charles-waite/ESP32-Matter-Environmental-Sensor/components/oled_ssd1306_tp/resources/DemoFrame2.jpg

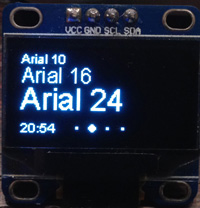
components/oled_ssd1306_tp/resources/DemoFrame2.jpg
