charles-waite/ESP32-Matter-Environmental-Sensor/components/oled_ssd1306_tp/resources/DemoFrame4.jpg

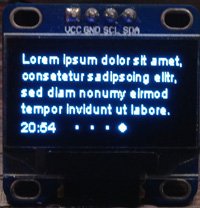
components/oled_ssd1306_tp/resources/DemoFrame4.jpg
