charles-waite/ESP32-Matter-Environmental-Sensor/main/chip_project_config.h

#pragma once

#define CHIP_DEVICE_CONFIG_DEVICE_VENDOR_NAME "Waite Design Labs"
#define CHIP_DEVICE_CONFIG_DEVICE_PRODUCT_NAME "WALL-Env Sensor"
#define CHIP_DEVICE_CONFIG_DEVICE_SOFTWARE_VERSION_STRING "0.6.0"
#define CHIP_DEVICE_CONFIG_DEFAULT_DEVICE_HARDWARE_VERSION_STRING "1.0"
