charles-waite/ESP32-Matter-Environmental-Sensor/components/BME68x_Sensor_library/examples/forced_mode/forced_mode.ino

/**
 * Copyright (C) 2021 Bosch Sensortec GmbH
 *
 * SPDX-License-Identifier: BSD-3-Clause
 * 
 */

#include "Arduino.h"
#include "bme68xLibrary.h"

#ifndef PIN_CS
#define PIN_CS SS
#endif

Bme68x bme;

/**
 * @brief Initializes the sensor and hardware settings
 */
void setup(void)
{
	SPI.begin();
	Serial.begin(115200);
	
	while (!Serial)
		delay(10);
		
	/* initializes the sensor based on SPI library */
	bme.begin(PIN_CS, SPI);

	if(bme.checkStatus())
	{
		if (bme.checkStatus() == BME68X_ERROR)
		{
			Serial.println("Sensor error:" + bme.statusString());
			return;
		}
		else if (bme.checkStatus() == BME68X_WARNING)
		{
			Serial.println("Sensor Warning:" + bme.statusString());
		}
	}
	
	/* Set the default configuration for temperature, pressure and humidity */
	bme.setTPH();

	/* Set the heater configuration to 300 deg C for 100ms for Forced mode */
	bme.setHeaterProf(300, 100);

	Serial.println("TimeStamp(ms), Temperature(deg C), Pressure(Pa), Humidity(%), Gas resistance(ohm), Status");
}

void loop(void)
{
	bme68xData data;

	bme.setOpMode(BME68X_FORCED_MODE);
	delayMicroseconds(bme.getMeasDur());

	if (bme.fetchData())
	{
		bme.getData(data);
		Serial.print(String(millis()) + ", ");
		Serial.print(String(data.temperature) + ", ");
		Serial.print(String(data.pressure) + ", ");
		Serial.print(String(data.humidity) + ", ");
		Serial.print(String(data.gas_resistance) + ", ");
		Serial.println(data.status, HEX);
	}
}
