charles-waite/ESP32-Matter-Environmental-Sensor/components/bsec2/examples/bme68x_demo_sample/sensor_manager.h

/*!
 * Copyright (c) 2021 Bosch Sensortec GmbH. All rights reserved.
 *
 * BSD-3-Clause
 *
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
 * 1. Redistributions of source code must retain the above copyright
 *    notice, this list of conditions and the following disclaimer.
 *
 * 2. Redistributions in binary form must reproduce the above copyright
 *    notice, this list of conditions and the following disclaimer in the
 *    documentation and/or other materials provided with the distribution.
 *
 * 3. Neither the name of the copyright holder nor the names of its
 *    contributors may be used to endorse or promote products derived from
 *    this software without specific prior written permission.
 *
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
 * @file	sensor_manager.h
 * @date	03 Jan 2024
 * @version	2.1.5
 * 
 * @brief	Header file for the sensor manager
 * 
 * 
 */

#ifndef SENSOR_MANAGER_H
#define SENSOR_MANAGER_H

/* Include of Arduino Core */
#include <Arduino.h>
#include <SdFat.h>
#include <RTClib.h>
#include <ArduinoJson.h>
#include <SPI.h>
#include <Wire.h>
#include "utils.h"
#include "demo_app.h"
#include <bme68xLibrary.h>
#include <commMux\commMux.h>

/* I2C-Expander masks */
#define I2C_EXPANDER_ADDR 				0x20
#define I2C_EXPANDER_OUTPUT_REG_ADDR 	0x01
#define I2C_EXPANDER_CONFIG_REG_ADDR 	0x03
#define I2C_EXPANDER_CONFIG_REG_MASK 	0x00
#define SPI_COMM_SPEED 					UINT32_C(4000000)
#define NUM_BME68X_UNITS				UINT8_C(8)
#define HEATER_TIME_BASE				UINT8_C(140)
#define MAX_HEATER_DURATION				UINT8_C(200)
#define GAS_WAIT_SHARED					UINT8_C(140)
/* Size of Json document in bytes */
#define JSON_DOC_SIZE 					UINT16_C(5000)

/*!
 * @brief : Class library that holds the functionality of the sensor manager
 */
class sensorManager
{
private:
	static bme68x_sensor _sensors[NUM_BME68X_UNITS];
	Bme68x 				bme68xSensors[NUM_BME68X_UNITS];
	bme68x_data 		 _field_data[3];

	StaticJsonDocument<JSON_DOC_SIZE>	_configDoc;
	
	/*!
	 * @brief : This function initializes the given BME688 sensor
	 * 
	 * @param[in] sensorNumber 	: The sensor number
	 * @param[in] sensorId 		: The sensor id
     * 
     * @return 0 on success, lessthan zero otherwise
	 */
	int8_t initialize_sensor(uint8_t sensor_number, uint32_t& sensor_id);
	/*!
	 * @brief : This function configures the heater settings of the sensor
	 * 
	 * @param[in] heaterProfileStr 	: The heater profile string id
	 * @param[in] dutyCycleStr 		: The duty cycle string id
	 * @param[in] heaterProfile 	: The heater profile structure
	 * @param[in] sensorNumber 		: The sensor number
     * 
     * @return  bme68x return code
	 */
	int8_t set_heater_profile(const String& heater_profile_str, const String& duty_cycle_str, 
	                        bme68x_heater_profile& heater_profile, uint8_t sensor_number);
	
	/*!
	 * @brief : This function configures the bme688 sensor
	 * 
	 * @param[in] heaterProfile : The heater profile structure
	 * @param[in] sensorNumber 	: The sensor number
     * 
     * @return  bme68x return code
	 */
	int8_t configure_sensor(bme68x_heater_profile& heater_profile, uint8_t sensor_number);
public:
	/*!
	 * @brief : This function retrieves the selected sensor.
	 * 
	 * @param[in] num : Sensor number
     * 
     * @return  Pointer to sensor if it exists, else nullptr
	 */
	static inline bme68x_sensor* get_sensor(uint8_t num)
	{
		bme68x_sensor* sensor = nullptr;

		if (num < NUM_BME68X_UNITS)
		{
			sensor = &_sensors[num];
		}
		return sensor;
	};
	
	/*!
	 * @brief : This function selects next readable bme688 sensor in given operation mode
	 * 
	 * @param[inout] num	: Reference to the sensor number
	 * @param[in] mode		: The sensor operation mode
     * 
     * @return  True if available
	 */
	static inline bool select_next_sensor(uint64_t& wake_up_time, uint8_t& num, uint8_t mode)
	{
		num = (uint8_t)0xFF;

		for (uint8_t i = 0; i < NUM_BME68X_UNITS; i++)
		{

			if ((_sensors[i].mode == mode) && (_sensors[i].wake_up_time < wake_up_time))
			{
				wake_up_time = _sensors[i].wake_up_time;
				num = i;
			}
		}
		
		if (num < NUM_BME68X_UNITS)
		{
			return true;
		}
		return false;
	}
	
	/*!
	 * @brief : This function schedules the next readable bme688 sensor
	 * 
	 * @param[inout] num : Reference to the sensor number
     * 
     * @return  True if available
	 */
	static inline bool schedule_sensor(uint8_t& num)
	{
		uint64_t wake_up_time = utils::get_tick_ms() + 20;
		return (select_next_sensor(wake_up_time, num, BME68X_PARALLEL_MODE) ||
		        select_next_sensor(wake_up_time, num, BME68X_SLEEP_MODE));
	};
	
    /*!
     * @brief : The constructor of the sensorManager class
     *        	Creates an instance of the class
     */
	sensorManager();
	
	/*!
     * @brief : This function initializes all bme688 sensors. It does not configure the sensor manager for data collection, 
	 *		 	the begin function should be used instead for this purpose.
     */
	demo_ret_code initialize_all_sensors();
	
	/*!
	 * @brief : This function configures the sensor manager using the provided config file.
	 * 
	 * @param[in] config : sensor configuration file
     * 
     * @return  error code
	 */
	demo_ret_code begin(const String& config);
	
	/*!
	 * @brief : This function retrieves the selected sensor data.
	 * 
	 * @param[in] num 	: Sensor number
	 * @param[in] data 	: Pointer to sensor data if it is available, else nullptr
     * 
     * @return  error code
	 */
	demo_ret_code collect_data(uint8_t num, bme68x_data* data[3]);
};

#endif
