charles-waite/ESP32-Matter-Environmental-Sensor/components/oled_ssd1306_tp/examples/SSD1306FontTryout/Dialog_plain_6.h

// Created by http://oleddisplay.squix.ch/ Consider a donation
// In case of problems make sure that you are using the font file with the correct version!
const char Dialog_plain_6[] PROGMEM = {
	0x06, // Width: 6
	0x08, // Height: 8
	0x20, // First Char: 32
	0xE0, // Numbers of Chars: 224

	// Jump Table:
	0xFF, 0xFF, 0x00, 0x02,  // 32:65535
	0x00, 0x00, 0x02, 0x02,  // 33:0
	0x00, 0x02, 0x02, 0x03,  // 34:2
	0x00, 0x04, 0x05, 0x05,  // 35:4
	0x00, 0x09, 0x04, 0x04,  // 36:9
	0x00, 0x0D, 0x06, 0x06,  // 37:13
	0x00, 0x13, 0x05, 0x05,  // 38:19
	0x00, 0x18, 0x02, 0x02,  // 39:24
	0x00, 0x1A, 0x02, 0x02,  // 40:26
	0x00, 0x1C, 0x02, 0x02,  // 41:28
	0x00, 0x1E, 0x03, 0x03,  // 42:30
	0x00, 0x21, 0x05, 0x05,  // 43:33
	0x00, 0x26, 0x02, 0x02,  // 44:38
	0x00, 0x28, 0x02, 0x02,  // 45:40
	0x00, 0x2A, 0x02, 0x02,  // 46:42
	0x00, 0x2C, 0x02, 0x02,  // 47:44
	0x00, 0x2E, 0x04, 0x04,  // 48:46
	0x00, 0x32, 0x04, 0x04,  // 49:50
	0x00, 0x36, 0x04, 0x04,  // 50:54
	0x00, 0x3A, 0x04, 0x04,  // 51:58
	0x00, 0x3E, 0x04, 0x04,  // 52:62
	0x00, 0x42, 0x04, 0x04,  // 53:66
	0x00, 0x46, 0x04, 0x04,  // 54:70
	0x00, 0x4A, 0x04, 0x04,  // 55:74
	0x00, 0x4E, 0x04, 0x04,  // 56:78
	0x00, 0x52, 0x04, 0x04,  // 57:82
	0x00, 0x56, 0x02, 0x02,  // 58:86
	0x00, 0x58, 0x02, 0x02,  // 59:88
	0x00, 0x5A, 0x05, 0x05,  // 60:90
	0x00, 0x5F, 0x05, 0x05,  // 61:95
	0x00, 0x64, 0x05, 0x05,  // 62:100
	0x00, 0x69, 0x03, 0x03,  // 63:105
	0x00, 0x6C, 0x06, 0x06,  // 64:108
	0x00, 0x72, 0x04, 0x04,  // 65:114
	0x00, 0x76, 0x04, 0x04,  // 66:118
	0x00, 0x7A, 0x04, 0x04,  // 67:122
	0x00, 0x7E, 0x05, 0x05,  // 68:126
	0x00, 0x83, 0x04, 0x04,  // 69:131
	0x00, 0x87, 0x03, 0x03,  // 70:135
	0x00, 0x8A, 0x05, 0x05,  // 71:138
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

	// Font Data:
	0x00,0x2C,	// 33
	0x00,0x0C,	// 34
	0x00,0x18,0x1C,0x38,0x18,	// 35
	0x00,0x2C,0x7E,0x3C,	// 36
	0x00,0x0C,0x2C,0x18,0x34,0x30,	// 37
	0x00,0x30,0x3C,0x34,0x30,	// 38
	0x00,0x0C,	// 39
	0x00,0x1C,	// 40
	0x00,0x1C,	// 41
	0x0C,0x0C,0x0C,	// 42
	0x00,0x08,0x08,0x3E,0x08,	// 43
	0x00,0x20,	// 44
	0x00,0x10,	// 45
	0x00,0x20,	// 46
	0x70,0x1C,	// 47
	0x00,0x3C,0x24,0x3C,	// 48
	0x00,0x24,0x3C,0x20,	// 49
	0x00,0x24,0x34,0x3C,	// 50
	0x00,0x24,0x2C,0x34,	// 51
	0x00,0x10,0x18,0x3C,	// 52
	0x00,0x2C,0x2C,0x3C,	// 53
	0x00,0x38,0x34,0x34,	// 54
	0x00,0x04,0x34,0x0C,	// 55
	0x00,0x34,0x2C,0x34,	// 56
	0x00,0x2C,0x2C,0x1C,	// 57
	0x00,0x28,	// 58
	0x00,0x28,	// 59
	0x00,0x08,0x08,0x1C,0x14,	// 60
	0x00,0x14,0x14,0x14,0x14,	// 61
	0x00,0x14,0x1C,0x08,0x08,	// 62
	0x00,0x04,0x24,	// 63
	0x00,0x38,0x54,0x74,0x14,0x08,	// 64
	0x20,0x1C,0x1C,0x20,	// 65
	0x00,0x3C,0x2C,0x34,	// 66
	0x00,0x18,0x24,0x24,	// 67
	0x00,0x3C,0x24,0x24,0x18,	// 68
	0x00,0x3C,0x2C,0x2C,	// 69
	0x00,0x3C,0x0C,	// 70
	0x00,0x18,0x24,0x2C,0x3C,	// 71
	0x00,0x3C,0x08,0x3C,	// 72
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
};
