charles-waite/ESP32-Matter-Environmental-Sensor/components/oled_ssd1306_tp/examples/SSD1306FontTryout/Dialog_plain_7.h

// Created by http://oleddisplay.squix.ch/ Consider a donation
// In case of problems make sure that you are using the font file with the correct version!
const char Dialog_plain_7[] PROGMEM = {
	0x07, // Width: 7
	0x09, // Height: 9
	0x20, // First Char: 32
	0xE0, // Numbers of Chars: 224

	// Jump Table:
	0xFF, 0xFF, 0x00, 0x02,  // 32:65535
	0x00, 0x00, 0x03, 0x03,  // 33:0
	0x00, 0x03, 0x03, 0x03,  // 34:3
	0x00, 0x06, 0x0B, 0x06,  // 35:6
	0x00, 0x11, 0x07, 0x04,  // 36:17
	0x00, 0x18, 0x0D, 0x07,  // 37:24
	0x00, 0x25, 0x09, 0x05,  // 38:37
	0x00, 0x2E, 0x03, 0x02,  // 39:46
	0x00, 0x31, 0x05, 0x03,  // 40:49
	0x00, 0x36, 0x05, 0x03,  // 41:54
	0x00, 0x3B, 0x07, 0x04,  // 42:59
	0x00, 0x42, 0x0B, 0x06,  // 43:66
	0x00, 0x4D, 0x03, 0x02,  // 44:77
	0x00, 0x50, 0x05, 0x03,  // 45:80
	0x00, 0x55, 0x03, 0x02,  // 46:85
	0x00, 0x58, 0x03, 0x02,  // 47:88
	0x00, 0x5B, 0x07, 0x04,  // 48:91
	0x00, 0x62, 0x07, 0x04,  // 49:98
	0x00, 0x69, 0x07, 0x04,  // 50:105
	0x00, 0x70, 0x07, 0x04,  // 51:112
	0x00, 0x77, 0x07, 0x04,  // 52:119
	0x00, 0x7E, 0x07, 0x04,  // 53:126
	0x00, 0x85, 0x07, 0x04,  // 54:133
	0x00, 0x8C, 0x07, 0x04,  // 55:140
	0x00, 0x93, 0x07, 0x04,  // 56:147
	0x00, 0x9A, 0x07, 0x04,  // 57:154
	0x00, 0xA1, 0x03, 0x02,  // 58:161
	0x00, 0xA4, 0x03, 0x02,  // 59:164
	0x00, 0xA7, 0x09, 0x06,  // 60:167
	0x00, 0xB0, 0x09, 0x06,  // 61:176
	0x00, 0xB9, 0x09, 0x06,  // 62:185
	0x00, 0xC2, 0x07, 0x04,  // 63:194
	0x00, 0xC9, 0x0D, 0x07,  // 64:201
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
	0x00,0x00,0x7C,0x00,0x44,0x00,0x44,0x00,0x38,	// 68
	0x00,0x00,0x7C,0x00,0x54,0x00,0x54,	// 69
	0x00,0x00,0x7C,0x00,0x14,0x00,0x14,	// 70
	0x00,0x00,0x38,0x00,0x44,0x00,0x54,0x00,0x74,	// 71
	0x00,0x00,0x7C,0x00,0x10,0x00,0x10,0x00,0x7C,	// 72
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
};
