charles-waite/ESP32-Matter-Environmental-Sensor/components/oled_ssd1306_tp/examples/SSD1306FontTryout/Dialog_plain_8.h

// Created by http://oleddisplay.squix.ch/ Consider a donation
// In case of problems make sure that you are using the font file with the correct version!
const char Dialog_plain_8[] PROGMEM = {
	0x08, // Width: 8
	0x0A, // Height: 10
	0x20, // First Char: 32
	0xE0, // Numbers of Chars: 224

	// Jump Table:
	0xFF, 0xFF, 0x00, 0x03,  // 32:65535
	0x00, 0x00, 0x03, 0x03,  // 33:0
	0x00, 0x03, 0x07, 0x04,  // 34:3
	0x00, 0x0A, 0x0B, 0x07,  // 35:10
	0x00, 0x15, 0x09, 0x05,  // 36:21
	0x00, 0x1E, 0x0F, 0x08,  // 37:30
	0x00, 0x2D, 0x0B, 0x06,  // 38:45
	0x00, 0x38, 0x03, 0x02,  // 39:56
	0x00, 0x3B, 0x05, 0x03,  // 40:59
	0x00, 0x40, 0x05, 0x03,  // 41:64
	0x00, 0x45, 0x07, 0x04,  // 42:69
	0x00, 0x4C, 0x0B, 0x07,  // 43:76
	0x00, 0x57, 0x04, 0x03,  // 44:87
	0x00, 0x5B, 0x05, 0x03,  // 45:91
	0x00, 0x60, 0x03, 0x03,  // 46:96
	0x00, 0x63, 0x05, 0x03,  // 47:99
	0x00, 0x68, 0x09, 0x05,  // 48:104
	0x00, 0x71, 0x07, 0x05,  // 49:113
	0x00, 0x78, 0x09, 0x05,  // 50:120
	0x00, 0x81, 0x09, 0x05,  // 51:129
	0x00, 0x8A, 0x09, 0x05,  // 52:138
	0x00, 0x93, 0x09, 0x05,  // 53:147
	0x00, 0x9C, 0x09, 0x05,  // 54:156
	0x00, 0xA5, 0x09, 0x05,  // 55:165
	0x00, 0xAE, 0x09, 0x05,  // 56:174
	0x00, 0xB7, 0x09, 0x05,  // 57:183
	0x00, 0xC0, 0x03, 0x03,  // 58:192
	0x00, 0xC3, 0x04, 0x03,  // 59:195
	0x00, 0xC7, 0x0B, 0x07,  // 60:199
	0x00, 0xD2, 0x0B, 0x07,  // 61:210
	0x00, 0xDD, 0x0B, 0x07,  // 62:221
	0x00, 0xE8, 0x07, 0x04,  // 63:232
	0x00, 0xEF, 0x0F, 0x08,  // 64:239
	0x00, 0xFE, 0x09, 0x05,  // 65:254
	0x01, 0x07, 0x09, 0x05,  // 66:263
	0x01, 0x10, 0x0B, 0x06,  // 67:272
	0x01, 0x1B, 0x0B, 0x06,  // 68:283
	0x01, 0x26, 0x09, 0x05,  // 69:294
	0x01, 0x2F, 0x07, 0x05,  // 70:303
	0x01, 0x36, 0x0B, 0x06,  // 71:310
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
